nuniesmith/volvo-vnl-cup-holder/pictures/box_inside_torsion_spring.jpg

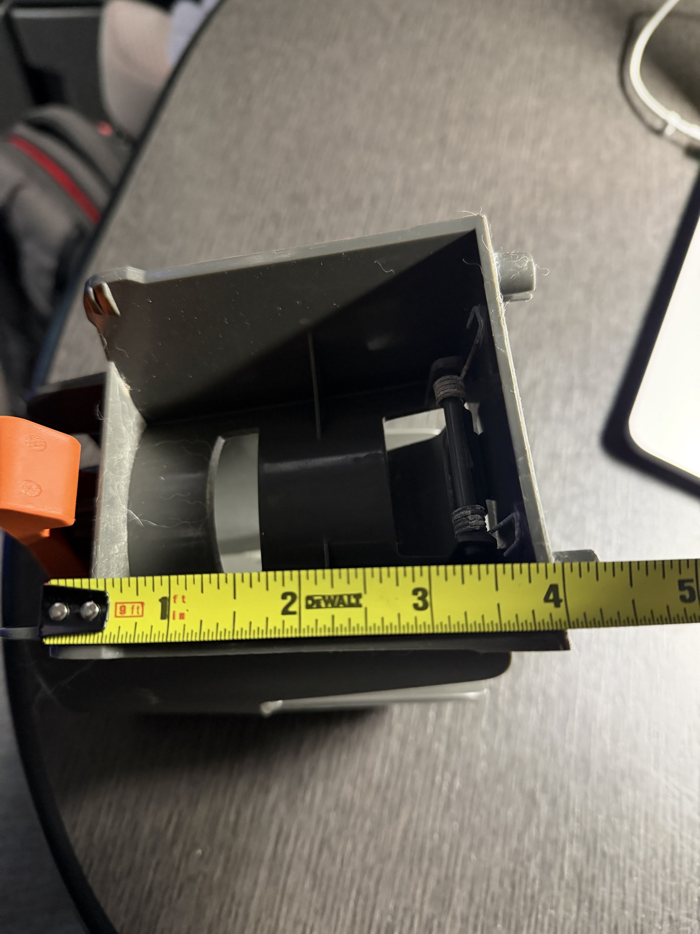
pictures/box_inside_torsion_spring.jpg
