nuniesmith/volvo-vnl-cup-holder/pictures/box_length_102_2mm.jpg

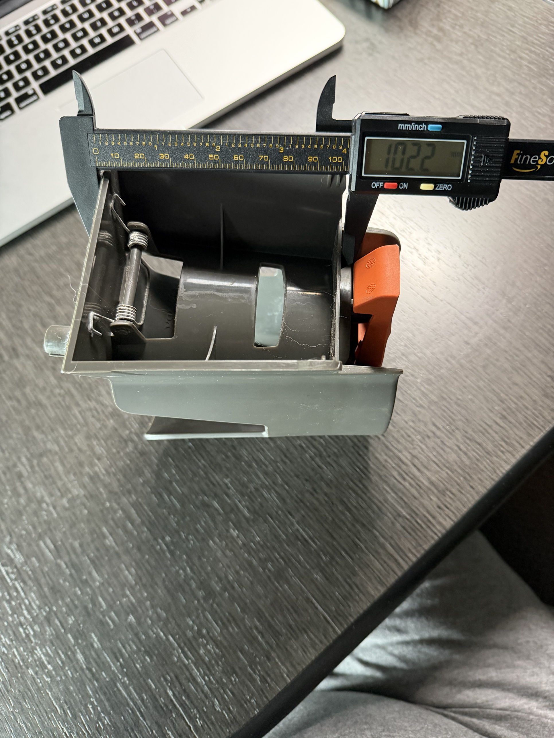
pictures/box_length_102_2mm.jpg
