nuniesmith/volvo-vnl-cup-holder/pictures/box_width_93_3mm.jpg

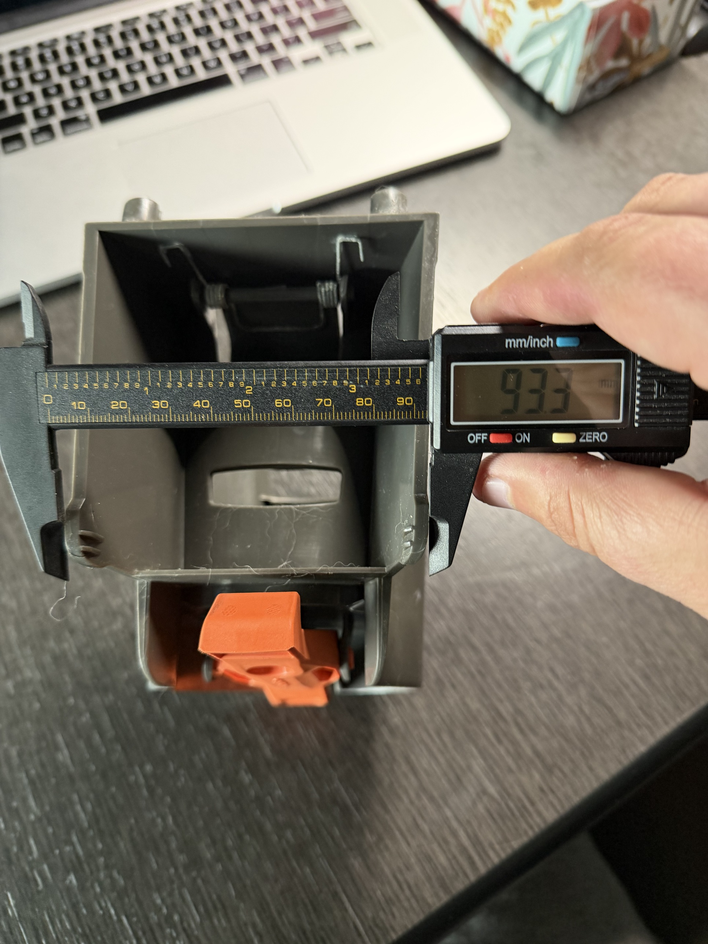
pictures/box_width_93_3mm.jpg
