nuniesmith/volvo-vnl-cup-holder/pictures/clip_end_17_6mm.jpg

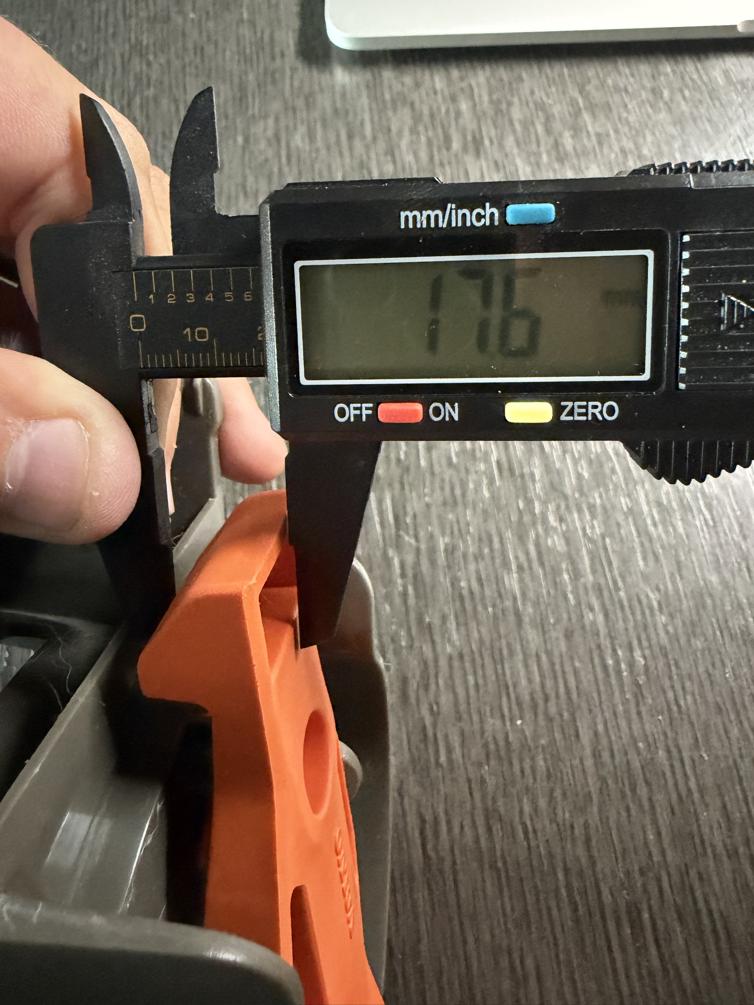
pictures/clip_end_17_6mm.jpg
