nuniesmith/volvo-vnl-cup-holder/pictures/clip_post_flange.jpg

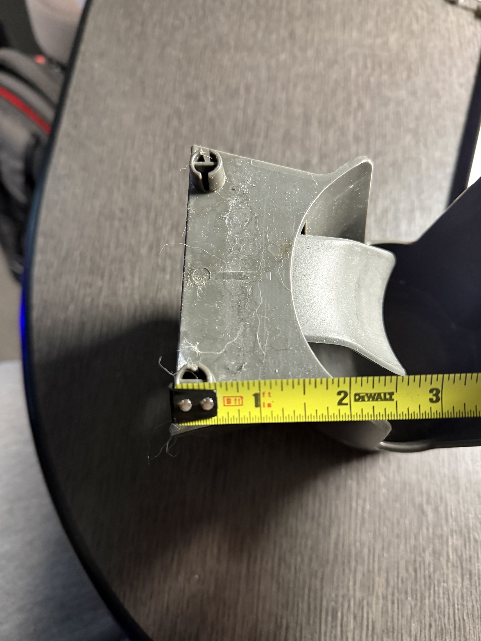
pictures/clip_post_flange.jpg
