nuniesmith/volvo-vnl-cup-holder/pictures/clip_socket_width_23_9mm.jpg

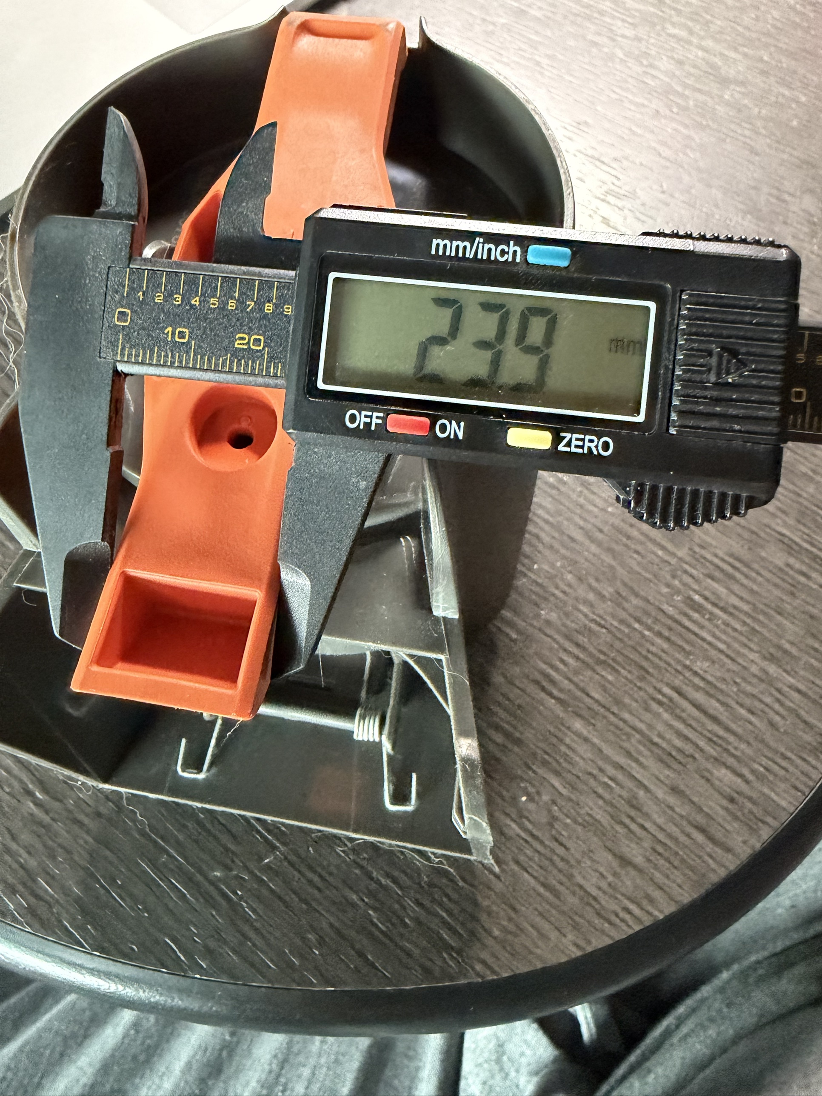
pictures/clip_socket_width_23_9mm.jpg
