nuniesmith/volvo-vnl-cup-holder/pictures/IMG_0149.JPEG

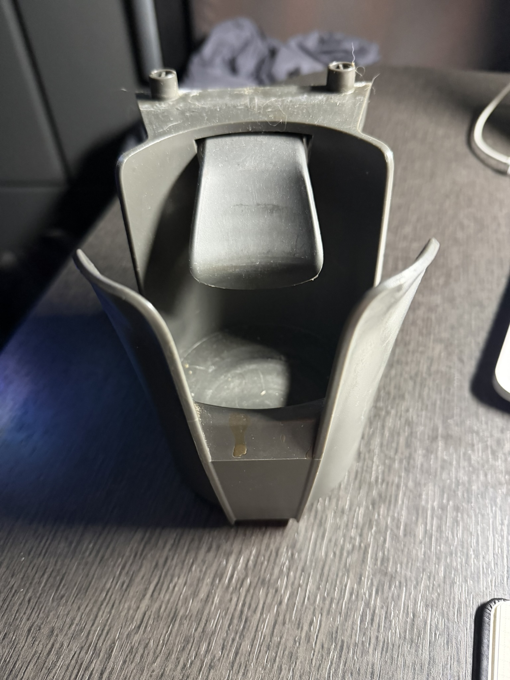
pictures/IMG_0149.JPEG
