nuniesmith/volvo-vnl-cup-holder/pictures/IMG_0150.JPEG

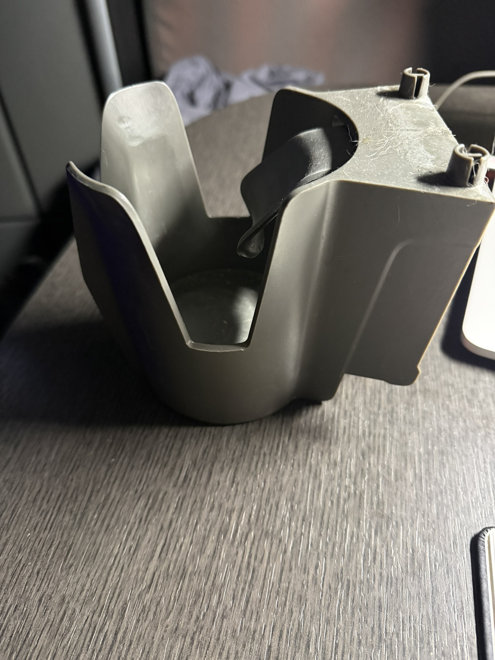
pictures/IMG_0150.JPEG
