nuniesmith/volvo-vnl-cup-holder/pictures/IMG_0151.JPEG

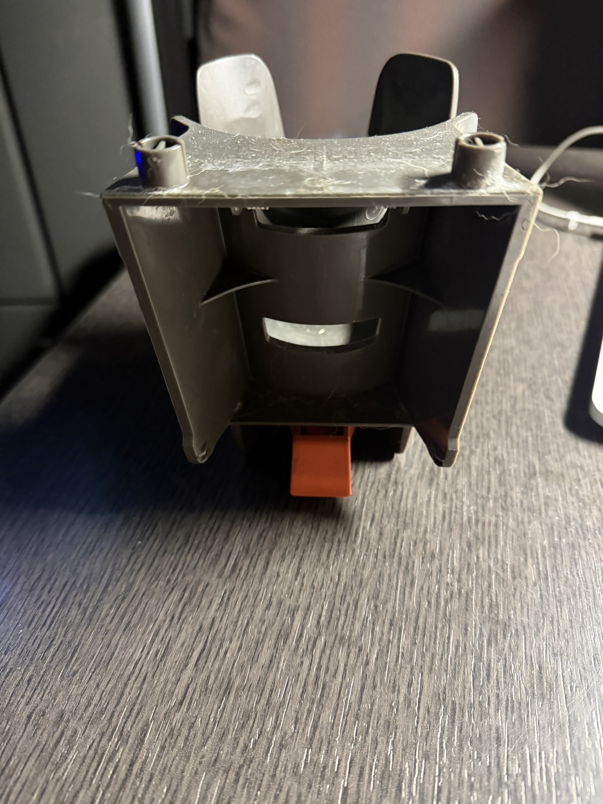
pictures/IMG_0151.JPEG
