nuniesmith/volvo-vnl-cup-holder/pictures/IMG_0152.JPEG

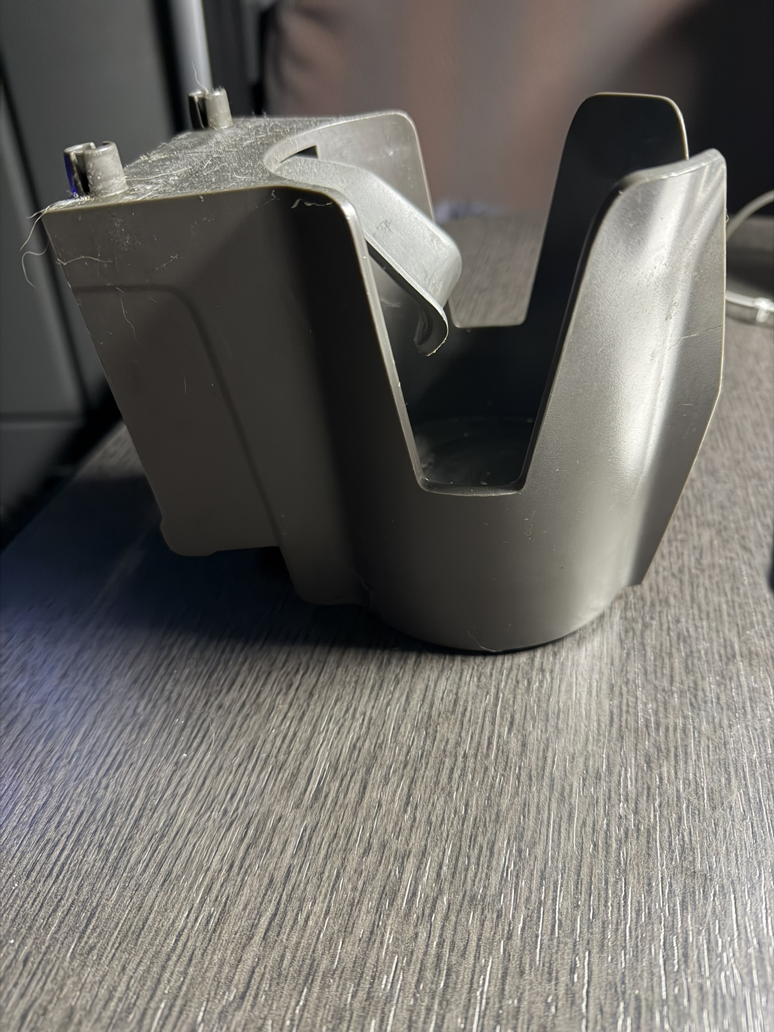
pictures/IMG_0152.JPEG
