nuniesmith/volvo-vnl-cup-holder/pictures/IMG_0153.JPEG

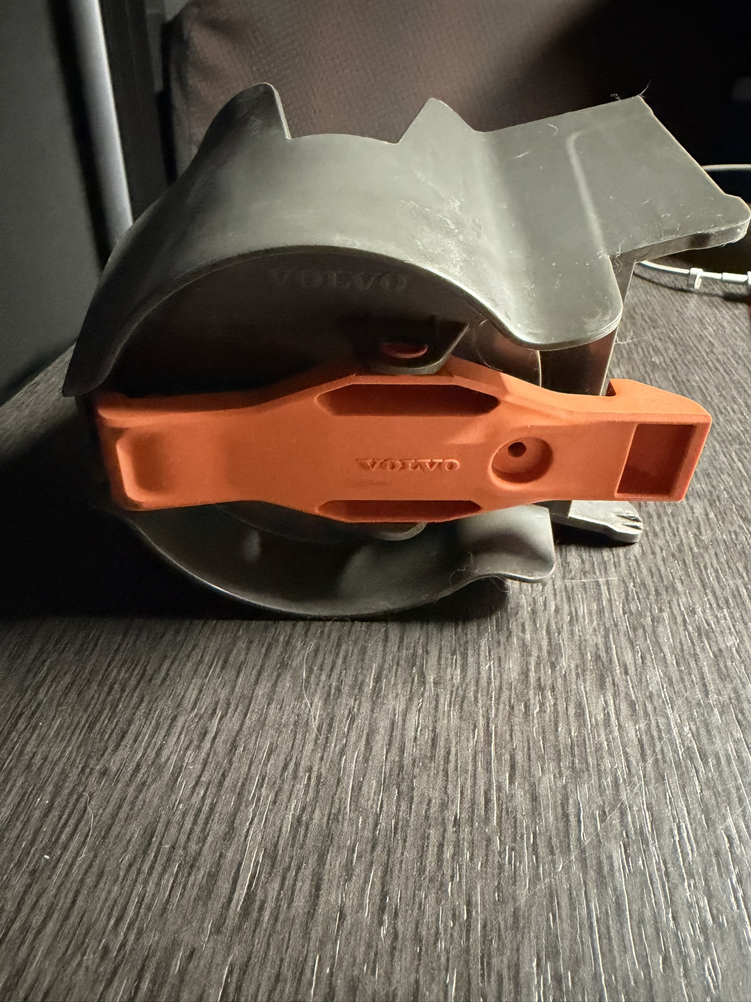
pictures/IMG_0153.JPEG
