nuniesmith/volvo-vnl-cup-holder/pictures/IMG_0154.JPEG

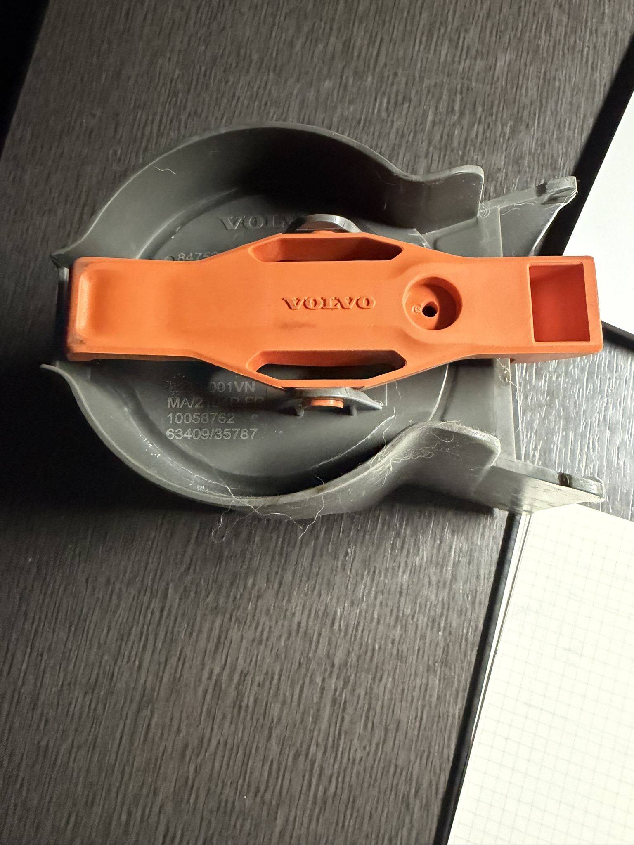
pictures/IMG_0154.JPEG
