nuniesmith/volvo-vnl-cup-holder/pictures/IMG_0155.JPEG

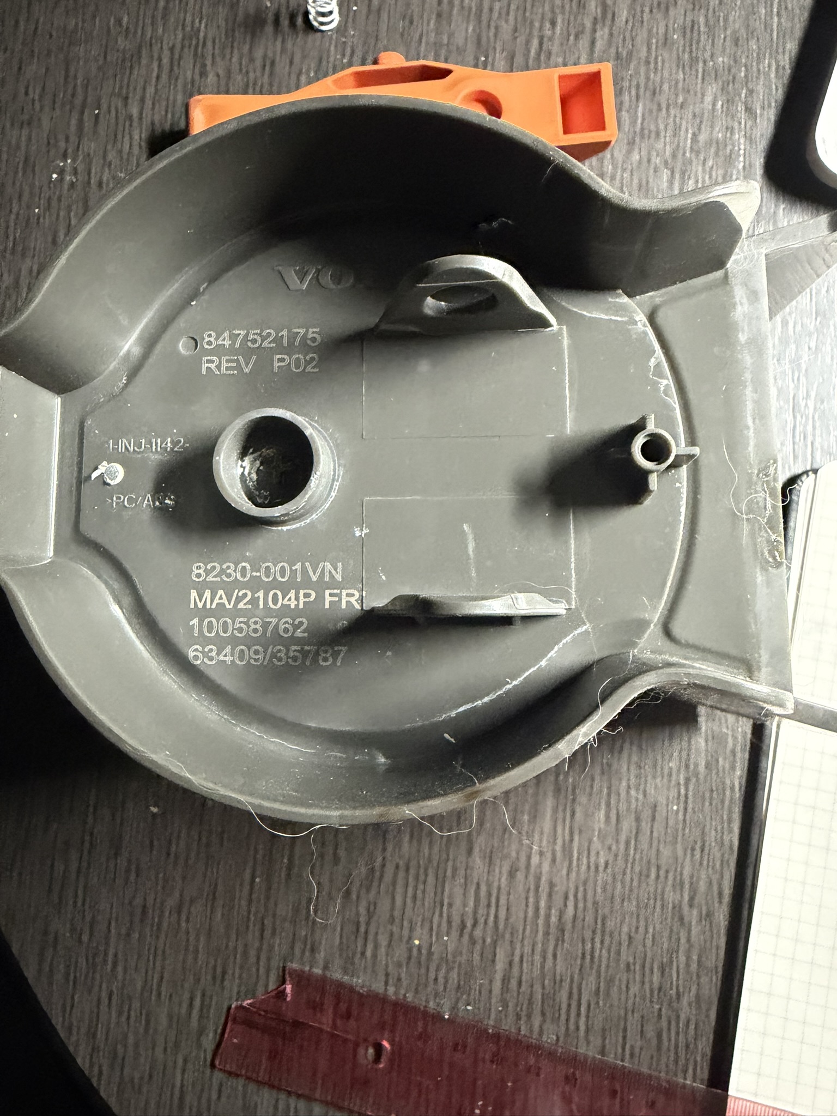
pictures/IMG_0155.JPEG
