nuniesmith/volvo-vnl-cup-holder/pictures/IMG_0156.JPEG

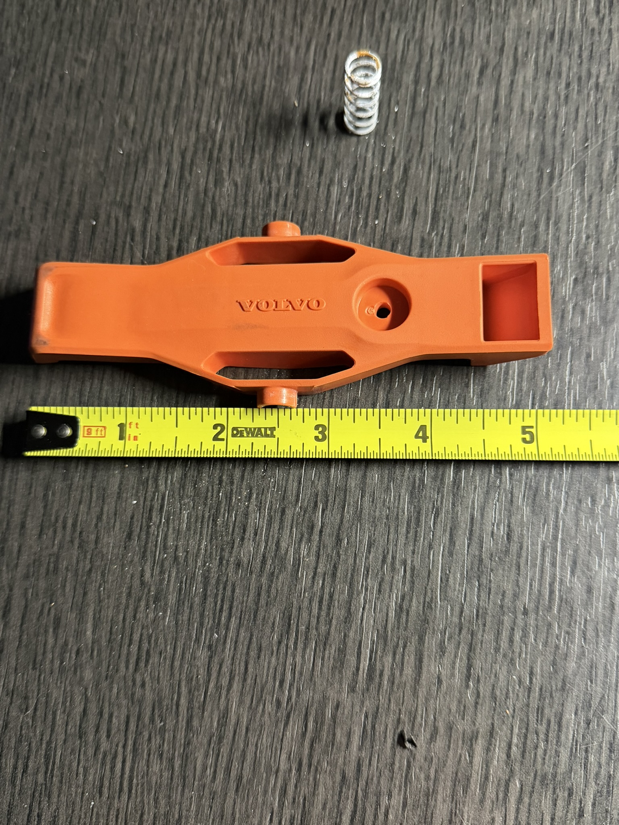
pictures/IMG_0156.JPEG
