nuniesmith/volvo-vnl-cup-holder/pictures/IMG_0157.JPEG

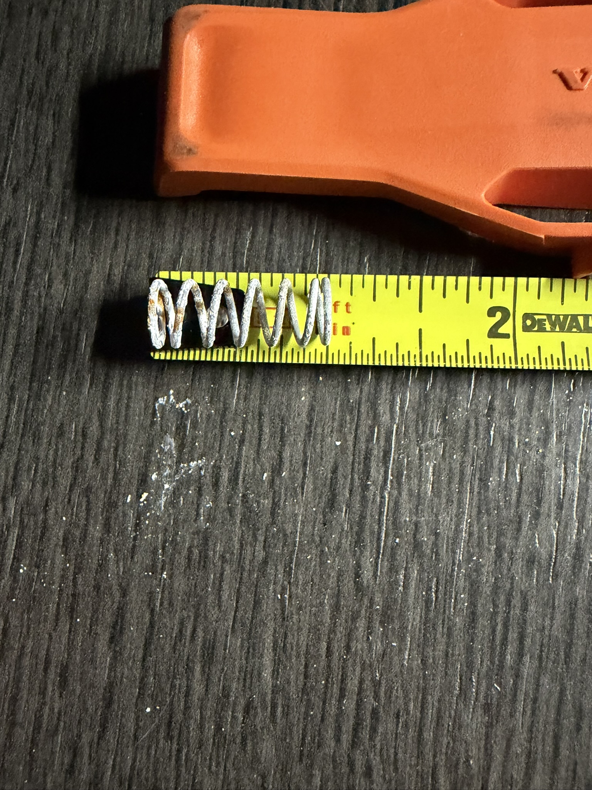
pictures/IMG_0157.JPEG
