nuniesmith/volvo-vnl-cup-holder/pictures/IMG_0158.JPEG

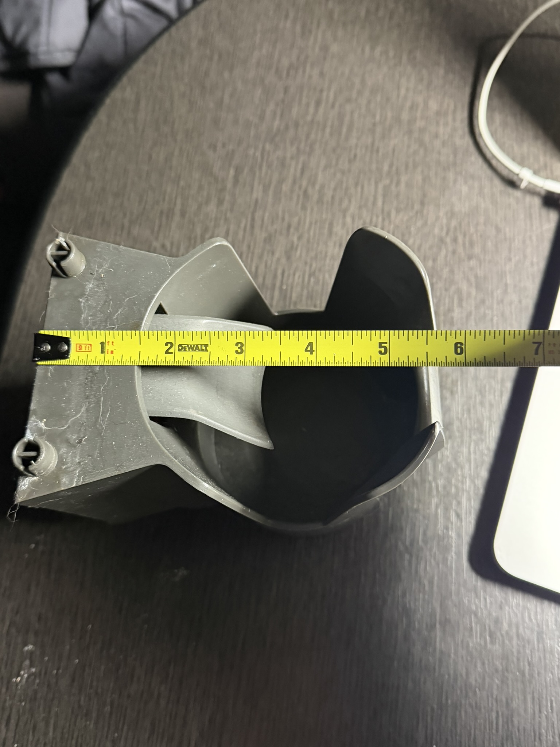
pictures/IMG_0158.JPEG
