nuniesmith/volvo-vnl-cup-holder/pictures/IMG_0159.JPEG

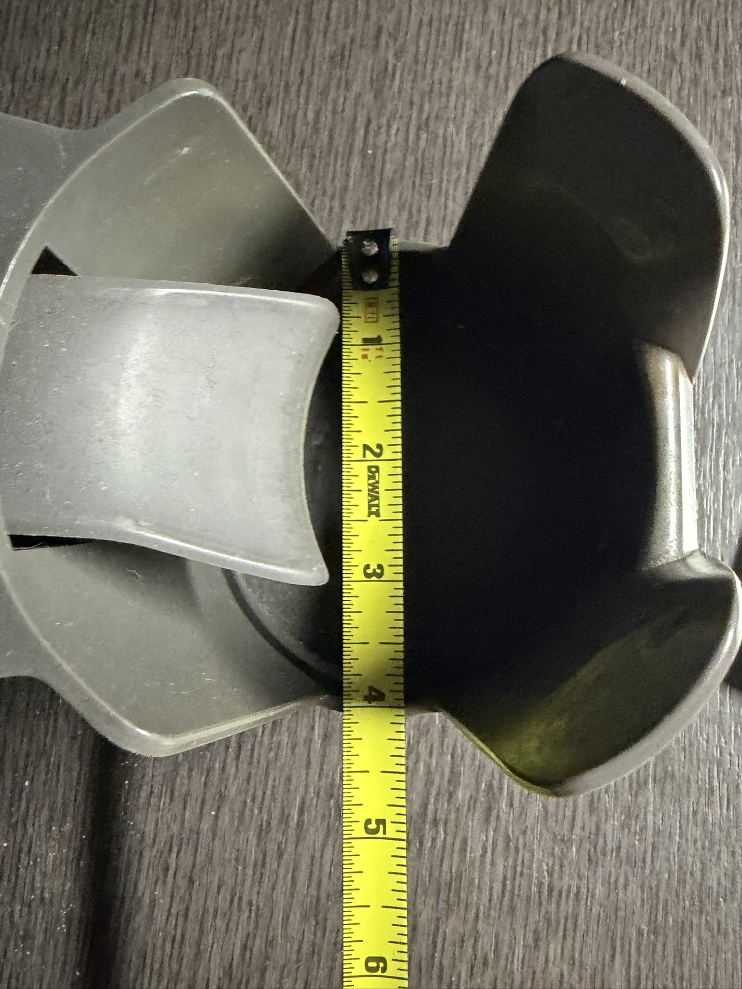
pictures/IMG_0159.JPEG
