nuniesmith/volvo-vnl-cup-holder/pictures/IMG_0160.JPEG

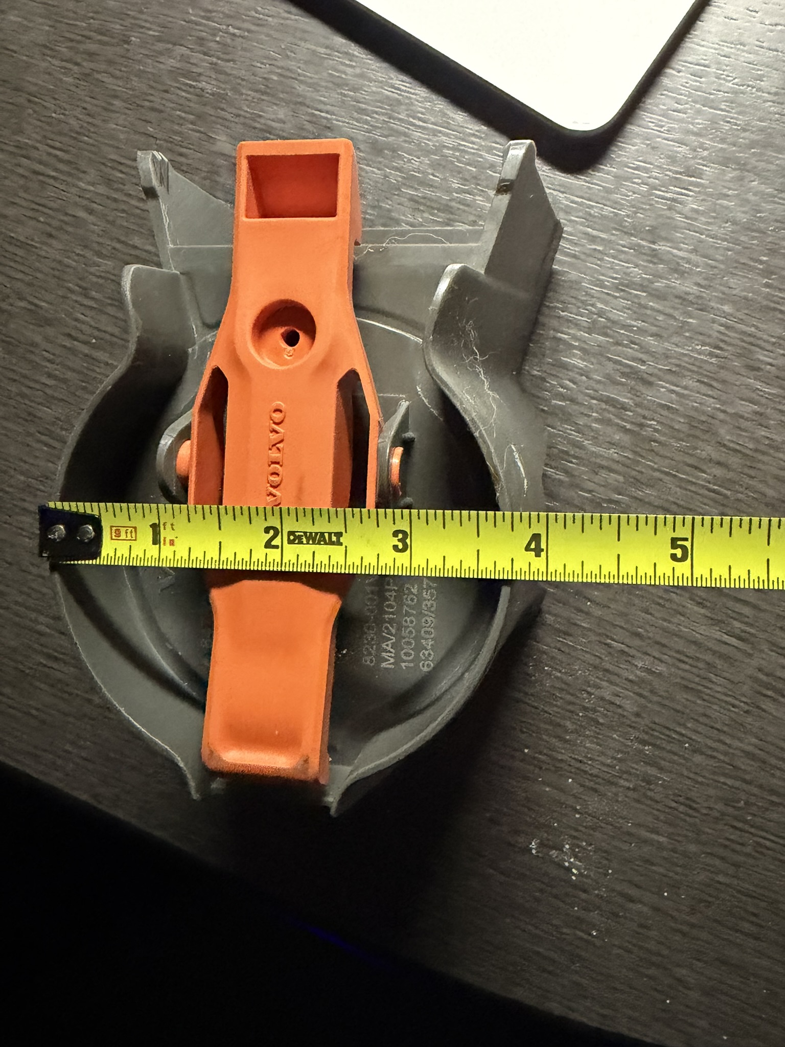
pictures/IMG_0160.JPEG
