nuniesmith/volvo-vnl-cup-holder/pictures/IMG_0161.JPEG

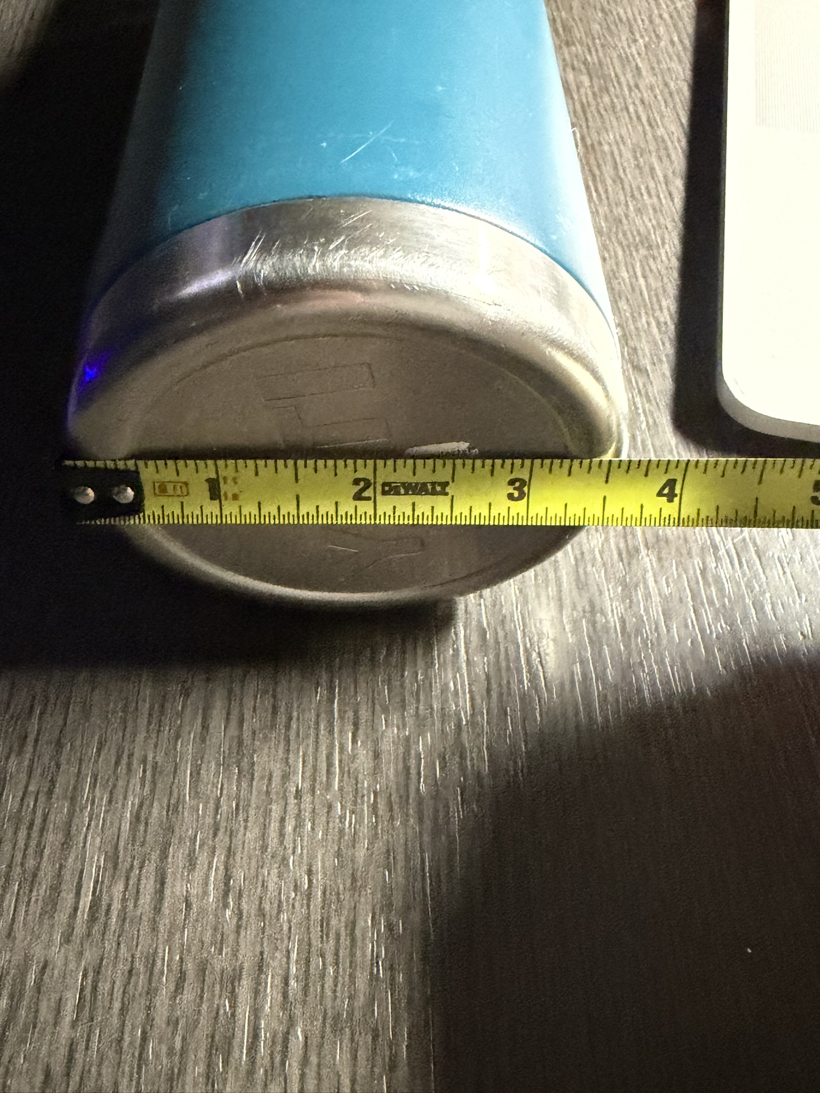
pictures/IMG_0161.JPEG
