nuniesmith/volvo-vnl-cup-holder/pictures/pivot_lugs_47_5mm.jpg

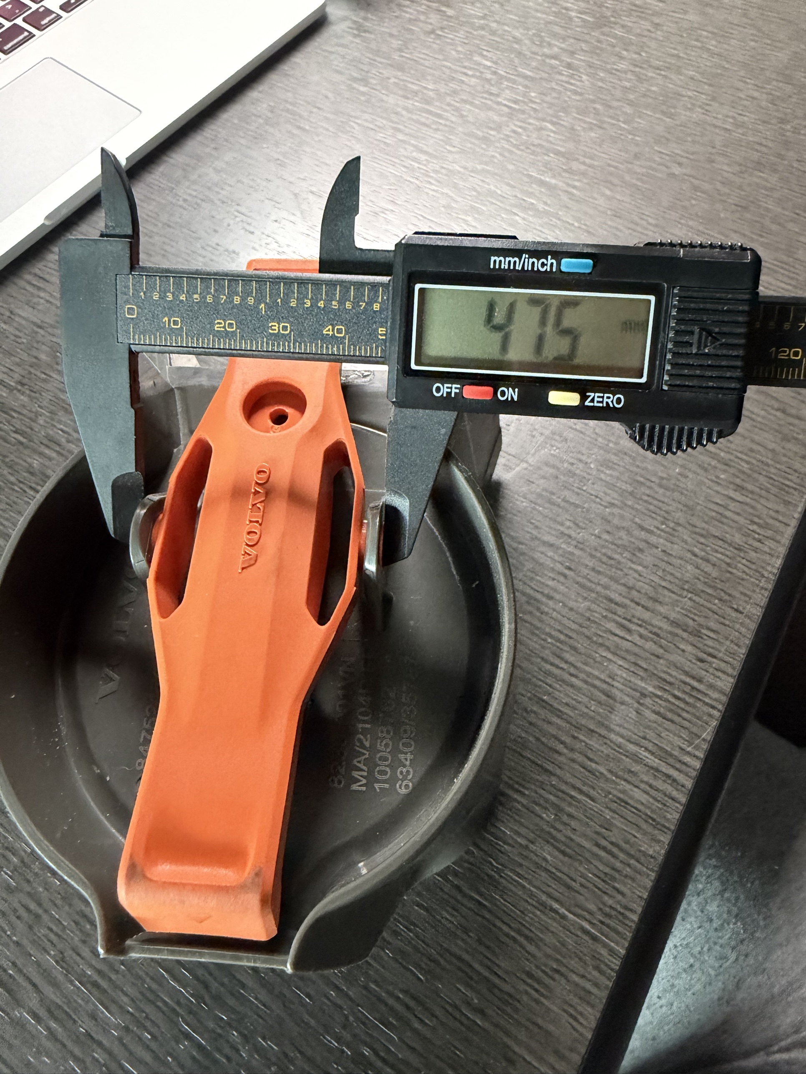
pictures/pivot_lugs_47_5mm.jpg
