nuniesmith/volvo-vnl-cup-holder/pictures/spring_kit.jpg

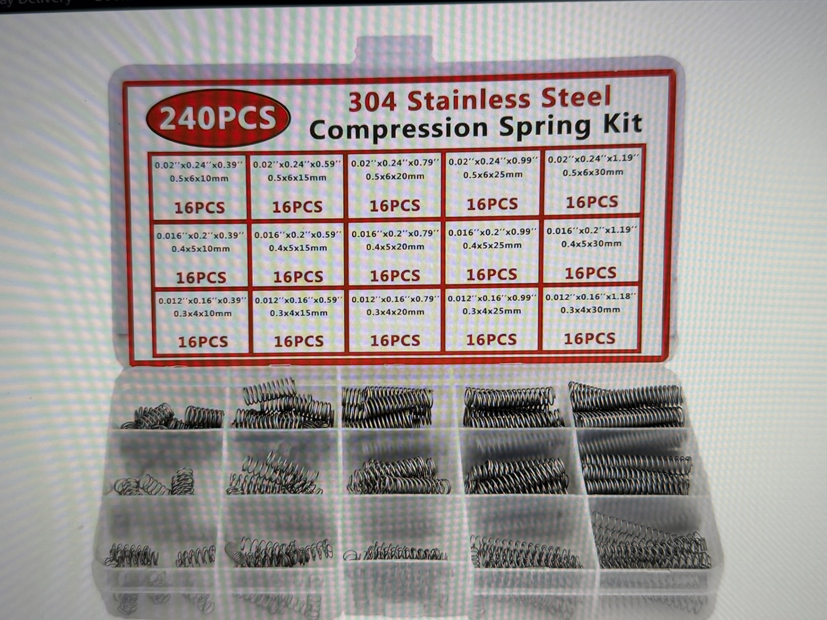
pictures/spring_kit.jpg
