nuniesmith/volvo-vnl-cup-holder/pictures/truck_mounting_shelf.jpg

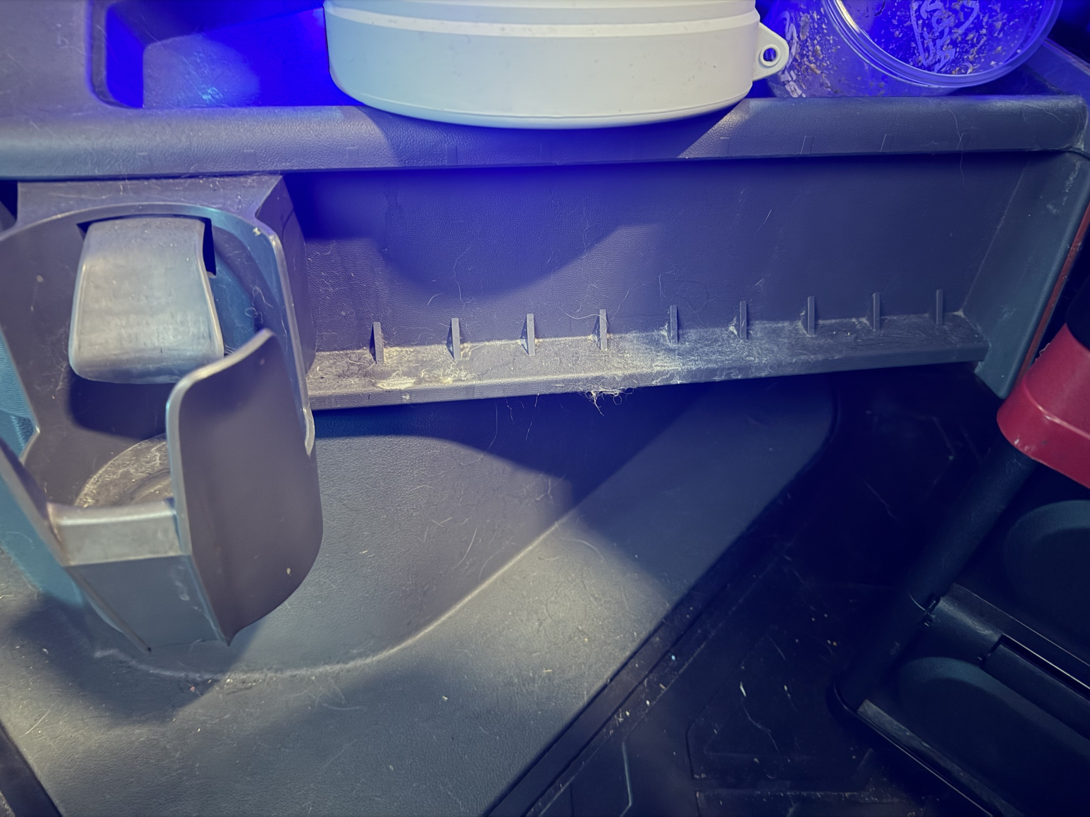
pictures/truck_mounting_shelf.jpg
