nuniesmith/volvo-vnl-cup-holder/pictures/two_holders_spacing.jpg

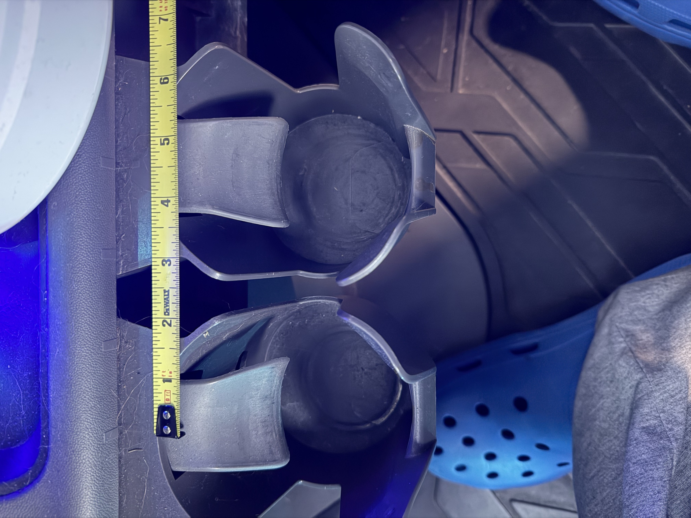
pictures/two_holders_spacing.jpg
