nuniesmith/volvo-vnl-cup-holder/pictures/stock_holder_installed.jpg

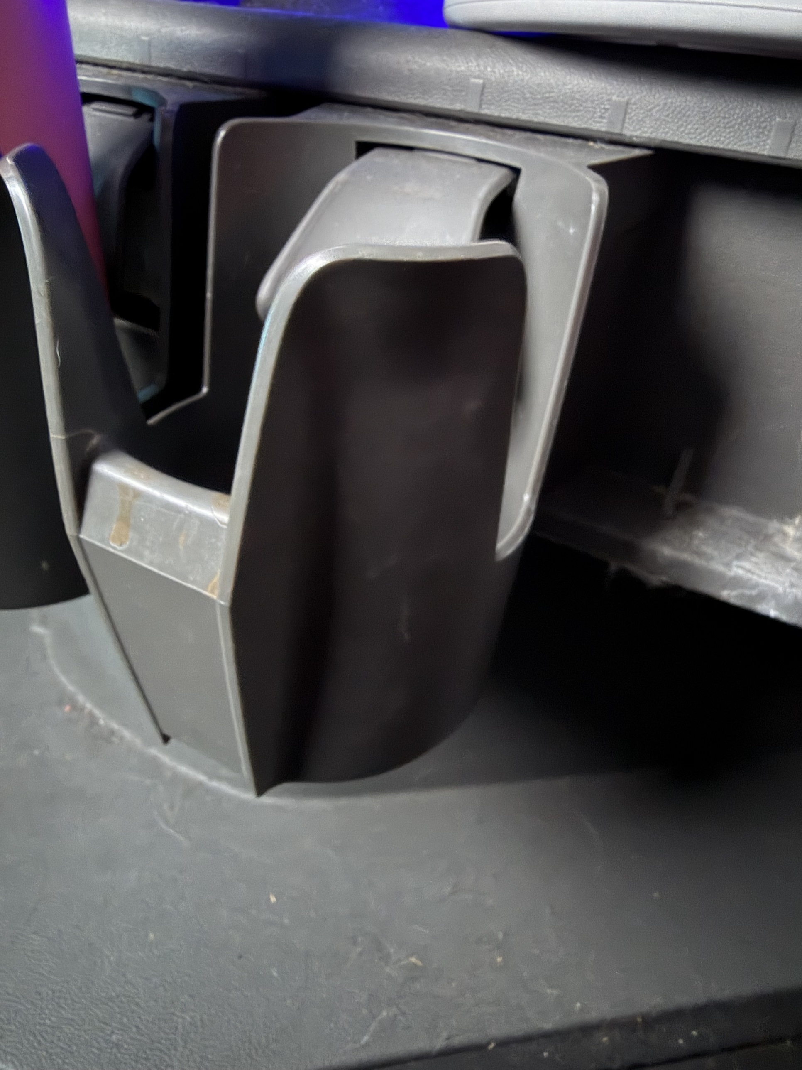
pictures/stock_holder_installed.jpg
