nuniesmith/volvo-vnl-cup-holder/docs/measure_posts.png

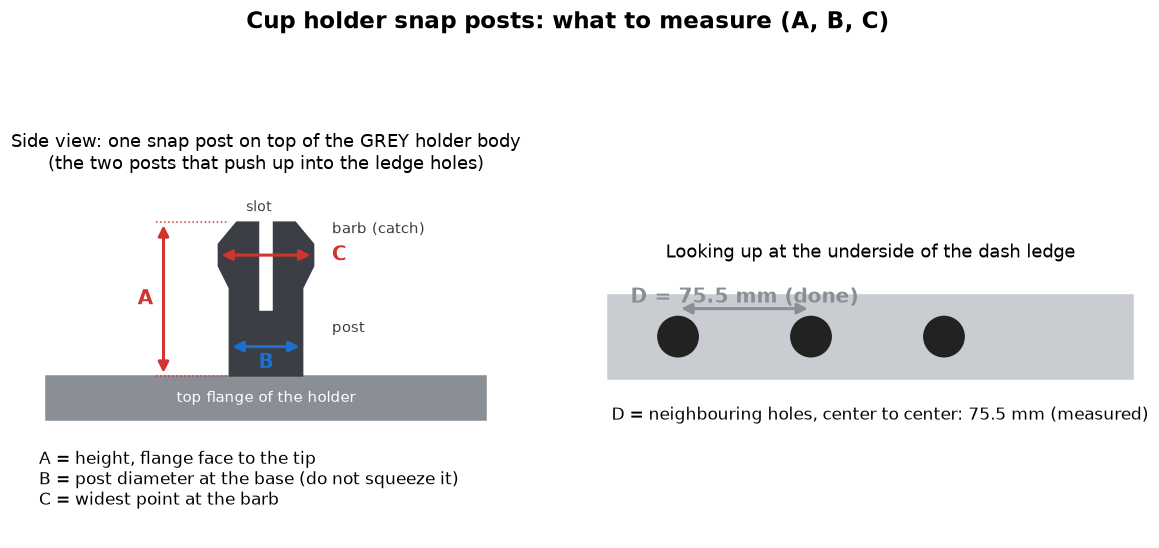
docs/measure_posts.png
